johnwinans/2067-Z8S180/fpga/nouveau-vdp99/top.v

//**************************************************************************
//
//    Copyright (C) 2024,2025  John Winans
//
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
//**************************************************************************

`default_nettype none

module top (
    input wire          hwclk,      // 25MHZ oscillator
    input wire          s1_n,
    output wire [7:0]   led,

    input wire [19:0]   a,
    inout wire [7:0]    d,          // bidirectional

    input wire          busack_n,
    output wire         busreq_n,

    output wire         ce_n,
    output wire         oe_n,
    output wire         we_n,

    output wire         dreq1_n,

    input wire          e,
    output wire         extal,
    input wire          phi,

    input wire          halt_n,

    output wire [2:0]   int_n,
    output wire         nmi_n,

    input wire          rd_n,
    input wire          wr_n,
    input wire          iorq_n,
    input wire          mreq_n,
    input wire          m1_n,

    output wire         reset_n,
    input wire          rfsh_n,
    input wire          st,
    input wire          tend1_n,
    output wire         wait_n,

    output wire         sd_mosi,
    output wire         sd_clk,
    output wire         sd_ssel_n,

    input wire          sd_miso,
    input wire          sd_det,

    input wire          joy1_up,
    input wire          joy1_dn,
    input wire          joy1_lt,
    input wire          joy1_rt,
    input wire          joy1_fire,
    input wire          joy1_btn2,

    output  wire [1:0]  vga_red,
    output  wire [1:0]  vga_grn,
    output  wire [1:0]  vga_blu,
    output  wire        vga_hsync,
    output  wire        vga_vsync,

    output  wire [2:0]  aout,       // hack for testing the AY-3-891x

    output wire [15:0]  tp          // handy-dandy test-point outputs
    );

    wire [7:0] vdp_dout;
    wire vdp_irq;

    localparam RAM_START = 20'h1000;

    assign tp = { iorq_wr_tick, iorq_rd_tick, phi, e, iorq_n, we_n, oe_n, ce_n, wr_n, rd_n, mreq_n, m1_n };
    //            93            90            87   84 82      80    78    75    73    63    61      56


    localparam HWCLK_FREQ       = 25000000;

    localparam NUM_BOOT_BRAMS   = 6;                  // Even number due to bug in yosys newer versions!
    localparam NUM_VRAM_BRAMS   = 32-NUM_BOOT_BRAMS;  // 32 total in ICE40HX4/8K, residual = VRAM

    // a boot ROM
    wire [7:0]  rom_data;           // ROM output data bus
    memory #( .RAM_SIZE(NUM_BOOT_BRAMS*512) ) rom ( .rd_clk(phi), .addr(a), .data(rom_data) );

    // consider debouncing s1_n using hwclk (no other clock possible)
    wire reset = ~s1_n || ~pll_locked;      // assert reset when PLL is starting up & unstable
    assign reset_n = ~reset;                // CPU reset

    // When the CPU is reading from the FPGA drive the bus, else tri-state it.
    reg [7:0] dout;                 // what to write to data bus when requested
    reg dbus_out;                   // 1 if the FPGA shoudl drive the data bus
    assign d = dbus_out ? dout : 8'bz;  // a tri-state driver

    reg rom_sel;                    // true when the boot ROM is enabled
    always @(posedge phi)
        if ( reset )
            rom_sel <= 1;               // after a hard reset, the boot ROM is enabled...
        else if ( ioreq_rd_fe_tick )    // until there is a read from IO port 0xfe
            rom_sel <= 0;

    // Determine if the FPGA will drive the data bus and with what
    // the CPU is reading from its data bus.
    always @(*) begin
        dbus_out = 1;
        dout = 8'bx;

        (* parallel_case *)     // no more than one case can match (one-hot)
        case (1)
        mreq_rom:       dout = rom_data;            // boot ROM memory
        ioreq_rd_f0:    dout = ioreq_rd_data;       // gpio input
        ioreq_rd_j3:    dout = ioreq_rd_data;       // J3 input
        ioreq_rd_j4:    dout = ioreq_rd_data;       // J4 input
        ioreq_rd_ay:    dout = ay_dout;       		// ay-3-8910
        ioreq_rd_vdp:   dout = vdp_dout;            // data from the VDP
        default:        dbus_out = 0;
        endcase
    end

    // 18.432MHZ = 57600 (when running at X/2)
    // 18.432MHZ = 115200 (when running at X/1)
    wire        pll_locked;             // true when the PLL has locked to target freq
    pll_25_18432 pll ( .clock_in(hwclk), .clock_out(extal), .locked(pll_locked) );


    // for read cycle: latch value on first phi falling edge after iorq becomes true:
    // fsm counting falling phi when rd is true & enable when count = 0 && iorq is true
    wire    iorq_rd_tick;
    iorq_rd_fsm rd_fsm (.reset(reset), .phi(phi), .iorq(~iorq_n), .rd(~rd_n), .rd_tick(iorq_rd_tick) );

    // for a write cycle: latch value on second phi falling edge after iorq becomes true:
    // fsm counting falling phi when wr is true and enable when count = 1
    wire    iorq_wr_tick;
    iorq_wr_fsm wr_fsm (.reset(reset), .phi(phi), .iorq(~iorq_n), .wr(~wr_n), .wr_tick(iorq_wr_tick) );


    // qualified asynchronous bus enable signals
    wire iorq_rd = ~iorq_n && ~rd_n;
    wire iorq_wr = ~iorq_n && ~wr_n;
    wire mem_rd = ~mreq_n && ~rd_n;
    wire mem_wr = ~mreq_n && ~wr_n;

    // IO address decoders (two variations):
    //  signal       = CPU asynchronous IO cycle
    //  signal_tick  = FPGA ff clock enable synchronized to phi
    //  NOTE: The address bus is stable during the iorq_rd/wr_tick periods.

    // gpio input
    wire ioreq_rd_f0 = iorq_rd && (a[7:0] == 8'hf0);                // gpio input
    wire ioreq_rd_f0_tick = iorq_rd_tick && (a[7:0] == 8'hf0);

//  wire ioreq_wr_f1 = iorq_wr && (a[7:0] == 8'hf1);                // gpio output
    wire ioreq_wr_f1_tick  = iorq_wr_tick && (a[7:0] == 8'hf1);

//  wire ioreq_rd_fe = iorq_rd && (a[7:0] == 8'hfe);                
    wire ioreq_rd_fe_tick = iorq_rd_tick && (a[7:0] == 8'hfe);      // flash select disable access port

    wire ioreq_rd_j3 = iorq_rd && (a[7:0] == 8'ha8);
    wire ioreq_rd_j3_tick = iorq_rd_tick && (a[7:0] == 8'ha8);      // joystick J3

    wire ioreq_rd_j4 = iorq_rd && (a[7:0] == 8'ha9);
    wire ioreq_rd_j4_tick = iorq_rd_tick && (a[7:0] == 8'ha9);      // joystick J4

    // B0 & B1 are the ay registers
    wire ioreq_wr_ay = iorq_wr && (a[7:1] == 8'hb0>>1);
    wire ioreq_rd_ay = iorq_rd && (a[7:1] == 8'hb0>>1);

    // ROM memory address decoder (address bus is 20 bits wide)
    wire mreq_rom = rom_sel && mem_rd && a[19:12] == 0;         // all top MSBs of bottom 4K are zero

    wire [7:0]  ay_dout;
    wire [2:0]  ay3891x_out;

    z80_ay3891x #(
        .CLK_FREQ(HWCLK_FREQ),
        ) ay (
        .reset(reset),
		.phi(phi),
        .clk(hwclk),
        .a0(a[0]),
        .cpu_wr(ioreq_wr_ay),
        .wdata(d),
        .cpu_rd(ioreq_rd_ay),
        .rdata(ay_dout),
        .aout(ay3891x_out)
        );

    assign aout = ay3891x_out;
    //assign aout = {2'b00, |ay3891x_out};    // OR the three channels into only the A channel output bit


    // The GPIO output latch
    reg [7:0] gpio_out;
    always @(negedge phi) begin
        if ( ioreq_wr_f1_tick )
            gpio_out <= d;
    end

    // This should be a 2-always state machine.
    reg [7:0] ioreq_rd_data;            // data value when reading an internal IO port
    always @(negedge phi) begin
        // ioreq_rd_data is an implied latch in here
        // XXX synchronize the joystick inputs at some point
        (* parallel_case *)     // no more than one case can match (one-hot)
        case (1)
        ioreq_rd_f0_tick:   ioreq_rd_data <= {sd_miso,sd_det,6'bx};
        ioreq_rd_j3_tick:   ioreq_rd_data <= { joy1_up, joy1_dn, joy1_rt, joy1_btn2, 1'b1, joy1_lt, ~vdp_irq, joy1_fire };
        ioreq_rd_j4_tick:   ioreq_rd_data <= { joy1_up, joy1_dn, joy1_rt, joy1_btn2, 1'b1, joy1_lt, 1'b1, joy1_fire };  // XXX
        endcase
    end

    assign sd_mosi = gpio_out[0];   // connect the GPIO output bits to the SD card pins
    assign sd_clk  = gpio_out[1];
    assign sd_ssel_n = gpio_out[2];

    assign busreq_n = 1'b1;     // de-assert /BUSREQ
    assign dreq1_n = 1'b1;      // de-assert /DREQ1
    assign int_n = { ~vdp_irq, 2'b11 };
    assign nmi_n = 1'b1;        // de-assert /NMI
    assign wait_n = 1'b1;       // de-assert /WAIT

    // Enable the static RAM on memory cycles when the data bus is driven by the FPGA
    // The address range that is used to enable the SRAM varies depending on if/when
    // the shadow ROM is being enabled.
    assign ce_n = ~(~mreq_n && ~dbus_out );
    assign oe_n = mreq_n | rd_n;
    assign we_n = mreq_n | wr_n;

    wire ioreq_rd_vdp = iorq_rd && (a[7:1] == 7'b1000000);  // true for ports 80 and 81
    wire ioreq_wr_vdp = iorq_wr && (a[7:1] == 7'b1000000);  // true for ports 80 and 81

`ifdef no_sync_vga
    wire [3:0] vdp_color;
    wire vdp_hsync;
    wire vdp_vsync;

    z80_vdp99 #( .VRAM_SIZE(NUM_VRAM_BRAMS*512) ) vdp (
        .reset(reset),
        .phi(phi),
        .pxclk(hwclk),
        .cpu_mode(a[0]),
        .cpu_din(d),
        .cpu_dout(vdp_dout),
        .irq(vdp_irq),
        .cpu_wr(ioreq_wr_vdp),
        .cpu_rd(ioreq_rd_vdp),
        .color(vdp_color),
        .hsync(vdp_hsync),
        .vsync(vdp_vsync)
    );

    // Remap the 4-bit VDP color codes to 6-bit RGB
    color_palette palette (
        .color(vdp_color),
        .red(vga_red),
        .grn(vga_grn),
        .blu(vga_blu)
    );

    assign vga_hsync = ~vdp_hsync;
    assign vga_vsync = ~vdp_vsync;
`else
    z80_vga99 #( .VRAM_SIZE(NUM_VRAM_BRAMS*512) ) vdp (
        .reset(reset),
        .phi(phi),
        .pxclk(hwclk),
        .cpu_mode(a[0]),
        .cpu_din(d),
        .cpu_dout(vdp_dout),
        .irq(vdp_irq),
        .cpu_wr(ioreq_wr_vdp),
        .cpu_rd(ioreq_rd_vdp),
        .red(vga_red),
        .grn(vga_grn),
        .blu(vga_blu),
        .hsync(vga_hsync),
        .vsync(vga_vsync)
    );
`endif

    // show some signals from the GPIO ports on the LEDs for reference
    assign led = {~sd_miso,sd_det,3'b111,~gpio_out[2:0]};

endmodule
