johnwinans/2067-Z8S180/fpga/nouveau-vdp99/z80_vdp99_tb.v

//**************************************************************************
//
//    Copyright (C) 2025  John Winans
//
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
//**************************************************************************

`timescale 1ns/1ns
`default_nettype none

module tb ();

    reg reset       = 1;
    reg phi         = 0;
    reg pxclk       = 0;

    reg iorq        = 0;
    reg rd          = 0;
    reg wr          = 0;
    reg [15:0] a    = 'hz;
    reg [7:0] d     = 'hz;

    reg t1_marker   = 0;    // used to make obvious which are T1 phi clocks


    wire [7:0]   cpu_dout;
    wire [3:0]   color;
    wire hsync;
    wire vsync;
    wire irq;

    z80_vdp99 uut (
        .reset(reset),
        .phi(phi),
        .pxclk(pxclk),
        .cpu_mode(a[0]),
        .cpu_din(d),
        .cpu_dout(cpu_dout),
        .cpu_wr(iorq && wr && (a[7:1] == 7'b1000000)),
        .cpu_rd(iorq && rd && (a[7:1] == 7'b1000000)),
        .color(color),
        .hsync(hsync),
        .vsync(vsync),
        .irq(irq)
    );

    localparam phi_period = (1.0/18432000)*1000000000; // clk1 is running at about 18.432MHZ
    localparam pxclk_period = (1.0/25000000)*1000000000; // clk2 is running at 25MHZ

    always #(phi_period/2) phi = ~phi;
    always #(pxclk_period/2) pxclk = ~pxclk;

    integer i;      // for loop iterator


    // A way to easily write to a VDP register in the test bench
    // to use this, set vdp_reg, and vdp_reg_value and then set do_reg_write true for one phi period
    //      vdp_reg <= 3;
    //      vdp_reg_value <= 12;
    //      do_reg_write <= 1;
    //      @(negedge do_reg_write);        // wait for this to set it back to 0

    reg [2:0]   vdp_reg         = 0;
    reg [7:0]   vdp_reg_value   = 0;
    reg         do_reg_write    = 0;

    always begin
        // wait for a tick on do_reg_write
        while (do_reg_write != 1'b1)
            @(posedge phi);

        @(posedge phi);         // wait for T1 rising of next bus cycle (opcode fetch)
        t1_marker <= 1;
        t1_marker <= #(phi_period) 0;
        @(posedge phi);         // T2 opcode fetch
        @(posedge phi);         // T3 opcode fetch

        // skip the operand fetch as if this were an OUT (nn),A instruction
        @(posedge phi);         // wait for T1 rising of next bus cycle (operand fetch)
        t1_marker <= 1;
        t1_marker <= #(phi_period) 0;
        @(posedge phi);         // T2 operand fetch
        @(posedge phi);         // T3 operand fetch

        // IO write cycle
        @(posedge phi);         // T1 rising
        t1_marker <= 1;
        t1_marker <= #(phi_period) 0;

        @(negedge phi);         // T1 falling
        a <= #20 8'h81;         // address valid after T1 rising and >5ns before IORQ
        d <= #25 vdp_reg_value; // data <25ns after T1 falling and >10ns before WR active
        iorq <= #25 1;          // iorq = <25ns after T1 falling
                                // rd = <25ns after T1 falling
        @(posedge phi);         // T2 rising
        wr <= #25 1;            // <25ns after T2 rising

        @(posedge phi);         // Tw rising
        @(posedge phi);         // T3 rising
        @(negedge phi);         // T3 falling

        iorq <= #1 0;           // iorq <25ns after T3 falling
        wr <= #1 0;             // wr <25ns after T3 falling
                                // rd <25ns after T3 falling

        @(negedge wr)           // be careful that wr does not happen after posedge phi here!!!
        a <= #5 'hz;            // >5ns after iorq & wr trailing
        d <= #10 'hz;           // >10ns after wr trailing



        @(posedge phi);         // wait for T1 rising of next bus cycle (opcode fetch)
        t1_marker <= 1;
        t1_marker <= #(phi_period) 0;
        @(posedge phi);         // T2 opcode fetch
        @(posedge phi);         // T3 opcode fetch

        // skip the operand fetch as if this were an OUT (nn),A instruction
        @(posedge phi);         // wait for T1 rising of next bus cycle (operand fetch)
        t1_marker <= 1;
        t1_marker <= #(phi_period) 0;
        @(posedge phi);         // T2 operand fetch
        @(posedge phi);         // T3 operand fetch

        // IO write cycle
        @(posedge phi);         // T1 rising
        t1_marker <= 1;
        t1_marker <= #(phi_period) 0;


        @(negedge phi);         // T1 falling
        // write to VDP register i
        a <= #20 8'h81;         // address valid after T1 rising and >5ns before IORQ
        d <= #25 8'h80+vdp_reg; // data <25ns after T1 falling and >10ns before WR active
        iorq <= #25 1;          // iorq = <25ns after T1 falling
                                // rd = <25ns after T1 falling
        @(posedge phi);         // T2 rising
        wr <= #25 1;            // <25ns after T2 rising

        @(posedge phi);         // Tw rising
        @(posedge phi);         // T3 rising

        do_reg_write <= 0;      // we will be done on the next rising phi

        @(negedge phi);         // T3 falling

        iorq <= #1 0;           // iorq <25ns after T3 falling
        wr <= #1 0;             // wr <25ns after T3 falling
                                // rd <25ns after T3 falling

        @(negedge wr)           // be careful that wr does not happen after posedge phi here!!!
        a <= #5 'hz;            // >5ns after iorq & wr trailing
        d <= #10 'hz;           // >10ns after wr trailing

    end




    initial begin
        $dumpfile( { `__FILE__, "cd" } );
        $dumpvars;

        // put some useful test data into the VRAM
        $readmemh( "z80_vdp99_tb.ram", uut.vdp.mem.vram );


        reset <= 1;
        #(phi_period*4);
        reset <= 0;
        #(phi_period*4);


        vdp_reg <= 0;
        vdp_reg_value <= 'h00;      // graphics mode 1
        //vdp_reg_value <= 'h02;      // graphics mode 2
        //vdp_reg_value <= 'h00;      // graphics mode 4
        do_reg_write <= 1;
        @(negedge do_reg_write);

        vdp_reg <= 1;
        vdp_reg_value <= 'h60;      // graphics mode 1, enable screen, IE
        //vdp_reg_value <= 'h68;      // graphics mode 4, enable screen, IE
        //vdp_reg_value <= 'h70;      // text mode, enable screen, IE
        //vdp_reg_value <= 'h50;      // text mode, enable screen, IE=0
        //vdp_reg_value <= 'h60;      // graphics mode 2, enable screen, IE
        do_reg_write <= 1;
        @(negedge do_reg_write);

        vdp_reg <= 2;
        vdp_reg_value <= 'h02;      // name table 0x0800 - 0x0bff
        do_reg_write <= 1;
        @(negedge do_reg_write);

        vdp_reg <= 3;
        vdp_reg_value <= 'h30;      // color table 0x0c00 - 0x0c20
        //vdp_reg_value <= 'h80;      // color table 0x2000 - 0x3800 (for mode 2 gfx)
        do_reg_write <= 1;
        @(negedge do_reg_write);

        vdp_reg <= 4;
        vdp_reg_value <= 'h00;      // pattern table 0x0000 - 0x07ff
        do_reg_write <= 1;
        @(negedge do_reg_write);


        vdp_reg <= 5;
        vdp_reg_value <= 'h1a;      // sprite attribute table 0x0d00 - 0x0d7f
        do_reg_write <= 1;
        @(negedge do_reg_write);

        vdp_reg <= 6;
        vdp_reg_value <= 'h02;      // sprite pattern table 0x1000 - 0x17ff
        do_reg_write <= 1;
        @(negedge do_reg_write);


        vdp_reg <= 7;
        vdp_reg_value <= 'h34;      // fg/bg colors
        do_reg_write <= 1;
        @(negedge do_reg_write);



//#(phi_period*100000);
//$finish;

        // wait until an entire frame has completed
        @(negedge vsync);

        // IRQ should have been asserted
        // Read from the VDP status register to see the IRQ status flag on data bus & then be reset

        @(posedge phi);

        @(negedge phi);         // T1 falling
        a <= #20 8'h81;         // address valid after T1 rising and >5ns before IORQ
        iorq <= #25 1;          // iorq = <25ns after T1 falling
        rd <= #25 1;            // rd = <25ns after T1 falling

        @(posedge phi);         // T2 rising
        @(posedge phi);         // Tw rising
        @(posedge phi);         // T3 rising
        @(negedge phi);         // T3 falling
        iorq <= #1 0;           // iorq <25ns after T3 falling
        rd <= #1 0;             // rd <25ns after T3 falling

        @(negedge iorq);
        a <= #5 'hz;            //  >5ns after iorq & rd trailing

        // wait until we can see the second frame begin
        //@(posedge uut.vdp.fsm.row_last);
        @(posedge uut.vdp.vid_active);
        @(posedge uut.vdp.vid_active);
        @(posedge uut.vdp.vid_active);
        @(posedge uut.vdp.vid_active);

        $finish;
    end

endmodule
