johnwinans/2067-Z8S180/fpga/vdp99/vram_tb.v

//**************************************************************************
//
//    Copyright (C) 2025  John Winans
//
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
//**************************************************************************

`timescale 1ns/1ns
`default_nettype none

module tb();

    localparam  VRAM_SIZE = 8192;
    localparam  VRAM_ADDR_WIDTH = $clog2(VRAM_SIZE);

    reg clk             = 0;        // pixel clock
    reg reset           = 0;
    reg wr_tick         = 0;
    reg rd_tick         = 0;
    reg mode            = 0;
    reg [7:0] din       = 'hz;
    reg [VRAM_ADDR_WIDTH-1:0] dma_addr = 'hx;
    reg dma_tick        = 0;

    wire [7:0] dout;

    vram #( .VRAM_SIZE(VRAM_SIZE) ) uut (
        .reset(reset),
        .clk(clk),
        .rd_tick(rd_tick),
        .wr_tick(wr_tick),
        .mode(mode),
        .din(din),
        .dout(dout),
        .dma_addr(dma_addr),
        .dma_rd_tick(dma_tick)
    );

    initial begin
        $dumpfile( { `__FILE__, "cd" } );
        $dumpvars;
    end
    
    localparam clk_period = (1.0/25000000)*1000000000; // clk is running at 25MHZ
    always #(clk_period/2) clk = ~clk;

    integer     i;
    integer     j;
    reg [7:0]   val8;       // a way to truncate the value of i

    initial begin

        #(clk_period*4);
        reset <= 1;
        #(clk_period*4);
        reset <= 0;
        #(clk_period*4);

        @(posedge clk);
        mode <= 1;          // mode 1 = address
        din <= 8'h00;       // address LSB
        wr_tick <= 1;

        @(posedge clk);
        mode <= 0;
        din <= 'hz;
        wr_tick <= 0;

        @(posedge clk);
        mode <= 1;          // mode 1 = address
        din <= 8'h40;       // address MSB (write mode)
        wr_tick <= 1;

        @(posedge clk);
        mode <= 0;
        din <= 'hz;
        wr_tick <= 0;


        // fill the VRAM with some data
        // note that while filling the first time, the read data is 'hx
//       for ( i=0; i<'h2000; i=i+1 ) begin
        for ( i=0; i<'h1fff; i=i+1 ) begin      // leave the last vram byte unset
            @(posedge clk);
            mode <= 0;      // mode 0 = data
            din <= i&'h0ff;
            wr_tick <= 1;

            @(posedge clk);
            mode <= 0;
            din <= 'hz;
            wr_tick <= 0;

            @(posedge clk);
        end

        // Wait to see the read-ahead getting data from the next address.
        // NOTE: This data may be X if the counter is not allowed to wrap around above.
        @(posedge clk);
        @(posedge clk);
        @(posedge clk);     // extra long time here to find easy in the waveform output
        @(posedge clk);
        @(posedge clk);
        @(posedge clk);

        // read it back
        mode <= 1;          // mode 1 = address
        din <= 8'h00;       // address LSB
        wr_tick <= 1;

        @(posedge clk);
        mode <= 1;          // mode 1 = address
        din <= 8'h00;       // address MSB (read mode)
        wr_tick <= 1;

        @(posedge clk);
        mode <= 0;          // mode 0 = data
        din <= 'hz;         // address MSB (read mode)
        wr_tick <= 0;

        // exagerated delay here to illustrate when dout is valid when idle
        @(posedge clk);
        @(posedge clk);

        for ( i=0; i<'h2000; i=i+1 ) begin
            val8 <= i;

//$display( "%8t vram[%4x]:%x", $time, i+'h20f, uut.vram[i+'h20f] );
            @(posedge clk);
            mode <= 0;      // mode 0 = data
            rd_tick <= 1;

            @(posedge clk);
            mode <= 0;
            rd_tick <= 0;

//$display( "%8t vram[%4x]:%x dout=%x i=%x", $time, i, uut.vram[i], dout, val8 );
            if ( dout !== val8 )
                $display( "memory readback failed: %8t vram[%4x]:%x dout:%x !== i:%x", $time, i, uut.vram[i], dout, val8 );

            @(posedge clk);
        end

        @(posedge clk);
        mode <= 0;
        din <= 'hz;
        wr_tick <= 0;
        rd_tick <= 0;
        @(posedge clk);
        @(posedge clk);
        @(posedge clk);




        // make sure that reading the status register will reset the register fsm
        
        // start setting up a new VRAM address
        mode <= 1;          // mode 1 = address
        din <= 8'h99;       // address LSB 
        wr_tick <= 1;
        rd_tick <= 0;

        @(posedge clk);
        // now abort the vram address setup by reading the status register
        mode <= 1;
        wr_tick <= 0;
        rd_tick <= 1;

        @(posedge clk);
        rd_tick <= 0;
        wr_tick <= 0;

        @(posedge clk);
        // now restart the vram address setting
        mode <= 1;          // mode 1 = address
        din <= 8'h11;       // address LSB 
        wr_tick <= 1;

        @(posedge clk);
        mode <= 1;          // mode 1 = address
        din <= 8'h33;       // address MSB (read mode)
        wr_tick <= 1;

        @(posedge clk);
        rd_tick <= 0;
        wr_tick <= 0;
        mode <= 0;
        din <= 'hz;
        
        @(posedge clk);
        @(posedge clk);
        @(posedge clk);
        mode <= 0;
        rd_tick <= 1;       // read 1 vram byte

        @(posedge clk);
        mode <= 0;
        rd_tick <= 0;

        @(posedge clk);
        mode <= 0;
        rd_tick <= 1;       // read a second vram byte

        @(posedge clk);
        mode <= 0;
        rd_tick <= 0;




        // DMA access tests
        @(posedge clk);
        mode <= 0;
        rd_tick <= 0;
        wr_tick <= 0;


        @(posedge clk);
        @(posedge clk);
        @(posedge clk);
        dma_addr <= 'h1100;
        dma_tick <= 1;

        @(posedge clk);
        dma_addr <= 'h1101;
        dma_tick <= 1;
        @(posedge clk);
        dma_addr <= 'h1102;
        dma_tick <= 1;

//        @(posedge clk);
//        dma_addr <= 0;
//        dma_tick <= 0;


        @(posedge clk);
        dma_addr <= 'hx;
        dma_tick <= 0;
        mode <= 0;
        rd_tick <= 1;       // read vram using the CPU interface
        @(posedge clk);
        mode <= 0;
        rd_tick <= 1;       // and another...  (this is illegally fast)
        @(posedge clk);
        mode <= 0;
        rd_tick <= 0;
        dma_addr <= 'h1103;
        dma_tick <= 1;

        // idle for a moment
        @(posedge clk);
        mode <= 0;
        rd_tick <= 0;
        wr_tick <= 0;
        dma_tick <= 0;
        dma_addr <= 'hx;
        din <= 'hz;
        @(posedge clk);
        @(posedge clk);

        @(posedge clk);     // another DMA read to show the address counter NOT advancing
        mode <= 0;
        rd_tick <= 0;
        wr_tick <= 0;
        dma_tick <= 1;
        dma_addr <= 'h1107;
        din <= 'hz;

        @(posedge clk);


        // what happens when BOTH dma_tick and rd_tick are true at the same time?
        mode <= 0;
        rd_tick <= 0;
        wr_tick <= 0;
        dma_tick <= 0;
        dma_addr <= 'hx;
        din <= 'hz;
        @(posedge clk);

        @(posedge clk);
        dma_addr <= 'h1108;
        dma_tick <= 1;
        rd_tick <= 1;

        @(posedge clk);
        mode <= 0;
        rd_tick <= 0;
        wr_tick <= 0;
        dma_tick <= 0;
        dma_addr <= 'hx;
        din <= 'hz;

        // waste time to make waveform easier to read
        @(posedge clk);
        @(posedge clk);
        @(posedge clk);


        // What happens If we assert dma_tick multiple periods with a rd_tick before the last dma_tick?
        // Observation: This is understandable but undesirable to do IRL.
        @(posedge clk);
        dma_addr <= 'h1109;
        dma_tick <= 1;
        rd_tick <= 0;

        @(posedge clk);
        dma_addr <= 'h110a;
        dma_tick <= 1;
        rd_tick <= 1;

        @(posedge clk);
        dma_addr <= 'h110b;
        dma_tick <= 1;
        rd_tick <= 0;



        // idle a while so can see the end of the waveform

        @(posedge clk);
        mode <= 0;
        rd_tick <= 0;
        wr_tick <= 0;
        dma_tick <= 0;
        dma_addr <= 'hx;
        din <= 'hz;

        #(clk_period*20);
        $finish;
    end

endmodule
