johnwinans/2067-Z8S180/fpga/vdp99/sprite.v

//**************************************************************************
//
//    Copyright (C) 2025  John Winans
//
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
//**************************************************************************

`timescale 1ns/1ns
`default_nettype none

/**
* Implement one TI99-style sprite.
*
* Pattern will have 16 bits loaded.  When rendering 8 bits, the LSB will be zero.
* (The TI99 size parameter is not handled here.)
* 1 VDP pixel = 2 pxclk periods.
* Note that mag can double the size to 32x32 max.
***************************************************************************/
module sprite 
    (
    input   wire        reset,          // active high
    input   wire        pxclk,          // 25MHZ VGA clock (2X the VDP clock)

    input   wire        vdp_col0_tick,  // when true, the next col will represent hpos_reg zero
    input   wire        mag,            // true when magnified mode (2X size VDP pixels)
    input   wire [8:0]  hpos,           // 0=left edge, 0xff=off right edge (in VDP pixel units)
    input   wire [15:0] pattern,        // pattern of the current row to render
    input   wire [3:0]  fg_color,       // foreground color
    input   wire        load_tick,      // true when time to load the pattern, hpos, fg_color,...

    output  wire [3:0]  color_out       // set to either fg_color or zero
    );

    reg         active_reg, active_next;            // sprite rendering is active
    reg [1:0]   pxvdp_reg, pxvdp_next;              // counts at pxclk rate
    reg         mag_reg, mag_next;                  // false = 1:1, true = 2:1 (magnify VDP pixels)
    reg [8:0]   hpos_reg, hpos_next;                // 0 = 32 VDP px to left of border
    reg         hpos_phase_reg, hpos_phase_next;    // used to remember if the hpos is even or odd
    reg [15:0]  pattern_reg, pattern_next;          // 16-bit row value that will shift out at hpos_reg
    reg [3:0]   fg_color_reg, fg_color_next;        // the sprite foreground color

    always @(posedge pxclk) begin
        if (reset) begin
            active_reg <= 0;
            pxvdp_reg <= 0;
            mag_reg <= 0;
            hpos_reg <= 0;
            hpos_phase_reg <= 0;
            pattern_reg <= 0;
            fg_color_reg <= 0;
        end else begin
            active_reg <= active_next;
            pxvdp_reg <= pxvdp_next;
            mag_reg <= mag_next;
            hpos_reg <= hpos_next;
            hpos_phase_reg <= hpos_phase_next;
            pattern_reg <= pattern_next;
            fg_color_reg <= fg_color_next;
        end
    end

    always @(*) begin
        active_next = active_reg;
        mag_next = mag_reg;
        hpos_next = hpos_reg;
        hpos_phase_next = hpos_phase_reg;
        pattern_next = pattern_reg;
        fg_color_next = fg_color_reg;

        pxvdp_next = pxvdp_reg+1;           // counts VGA pixels (in spite of the name)

        if (load_tick) begin
            active_next = 0;
            mag_next = mag;
            hpos_next = hpos;
            hpos_phase_next = hpos[0];      // used when smag=1 to shift on even/odd columns
            pattern_next = pattern;
            fg_color_next = fg_color;
        end

        if (vdp_col0_tick) begin
            active_next = 1;                // start counting/rendering the sprite
            pxvdp_next = 0;                 // jam sync the phase so start at zero
        end 
        if (active_reg && pxvdp_reg[0]) begin
            // skip hpos_reg pixels and then start showing the pattern bits
            if (hpos_reg != 0) begin
                hpos_next = hpos_reg-1;
            end else begin
                // mag_reg doubles the size of the pixels, shift 1/2 as often
                if ( ~mag_reg )
                    pattern_next = { pattern_reg[14:0], 1'b0 };
                else if ( pxvdp_reg[1] == ~hpos_phase_reg )         // shifting from an even or odd hpos?
                    pattern_next = { pattern_reg[14:0], 1'b0 };
            end
        end
    end

    // Sprite is showing when active_reg & the pattern_reg MSb is 1.
    // Note: After the sprite is done, pattern_reg will be 0. So no need to 'stop' this.
    assign color_out = (active_reg && hpos_reg==0 && pattern_reg[15]) ? fg_color_reg : 0;

endmodule
