johnwinans/2067-Z8S180/fpga/nouveau-vdp99/color_palette.v

//**************************************************************************
//
//    Copyright (C) 2025  John Winans
//
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
//**************************************************************************

`timescale 1ns/1ns
`default_nettype none

// a color palette for mapping the TI99 colors to a 6-bit RGB dac

module color_palette (
    input wire [3:0]    color,
    output reg [1:0]   red,         // these are reg because I am lazy
    output reg [1:0]   grn,
    output reg [1:0]   blu
    );

    always @(*) begin
        case(color)
        4'h0: begin     // black
            red = 0;
            grn = 0;
            blu = 0;
        end
        4'h1: begin     // black
            red = 0;
            grn = 0;
            blu = 0;
        end
        4'h2: begin     // mid grn
            red = 0;
            grn = 2;
            blu = 0;
        end
        4'h3: begin     // lt grn
            red = 0;
            grn = 3;
            blu = 0;
        end
        4'h4: begin     // drk blu
            red = 0;
            grn = 0;
            blu = 1;
        end
        4'h5: begin     // lt blu
            red = 0;
            grn = 0;
            blu = 3;
        end
        4'h6: begin     // drk red
            red = 1;
            grn = 0;
            blu = 0;
        end
        4'h7: begin     // cyan
            red = 0;
            grn = 3;
            blu = 3;
        end
        4'h8: begin     // med red
            red = 2;
            grn = 0;
            blu = 0;
        end
        4'h9: begin     // lt red
            red = 3;
            grn = 0;
            blu = 0;
        end
        4'ha: begin     // drk yel
            red = 1;
            grn = 1;
            blu = 0;
        end
        4'hb: begin     // lt yel
            red = 3;
            grn = 3;
            blu = 0;
        end
        4'hc: begin     // drk grn
            red = 0;
            grn = 1;
            blu = 0;
        end
        4'hd: begin     // magenta
            red = 3;
            grn = 0;
            blu = 3;
        end
        4'he: begin     // gry
            red = 1;
            grn = 1;
            blu = 1;
        end
        4'hf: begin     // wht
            red = 3;
            grn = 3;
            blu = 3;
        end
        endcase
    end

endmodule
