johnwinans/2067-Z8S180/fpga/vdp99/reg_ifce_tb.v

//**************************************************************************
//
//    Copyright (C) 2025  John Winans
//
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
//**************************************************************************

`timescale 10ns/1ns

module tb();

    reg clk;        // pixel clock
    reg reset;
    reg wr_tick;
    reg rd_tick;
    reg [7:0] din;

    vdp_reg_ifce uut (
        .clk(clk),
        .reset(reset),
        .wr_tick(wr_tick),
        .rd_tick(rd_tick),
        .din(din)
    );

    initial begin
        $dumpfile("reg_ifce_tb.vcd");
        $dumpvars;
    end
    
    always #1 clk = ~clk;

    initial begin
        clk = 0;
        wr_tick = 0;
        rd_tick = 0;
        din = 'hz;
        reset = 1;
        #5;

        reset <= 0;
        #4;

        //#0.3;           // exaggerate the tick changes after the rising edges

        // reg0 = 0xee
        din <= 'hee;
        wr_tick <= 1;
        #2;
        wr_tick <= 0;
        din <= 'hz;
        #2;
        din <= 'h80;     // write into reg 0
        wr_tick <= 1;
        #2;
        wr_tick <= 0;
        din <= 'hz;
        #2;

        // reg3 = 0x33
        din <= 'h33;
        wr_tick <= 1;
        #2;
        wr_tick <= 0;
        din <= 'hz;
        #2;
        din <= 'h83;     // write into reg 3
        wr_tick <= 1;
        #2;
        wr_tick <= 0;
        din <= 'hz;
        #2;

        // rapid-fire writes
        din <= 'h44;
        wr_tick <= 1;
        #2;
        din <= 'h84;
        #2;
        din <= 'h55;
        #2;
        din <= 'h85;
        #2;
        din <= 'h66;
        #2;
        din <= 'h86;
        #2;
        wr_tick <= 0;
        din <= 'hz;
        #4;

        // test rm0 reset the 2-state write register toggler
        din <= 'h22;
        wr_tick <= 1;
        #2;
        wr_tick <= 0;
        din <= 'hz;
        #2;

        rd_tick <= 1;
        #2;
        rd_tick <= 0;
        din <= 'hz;
        #2;

        // make sure it still works (we didn't get it stuck)
        din <= 'h11;
        wr_tick <= 1;
        #2;
        din <= 'h81;
        #2;
        wr_tick <= 0;
        din <= 'hz;
        #2;

        // make sure we can CHANGE a value that has already been written
        din <= 'hf6;
        wr_tick <= 1;
        #2;
        din <= 'h86;
        #2;
        wr_tick <= 0;
        din <= 'hz;
        #2;

        // make sure that rm0 is OK when not done in state 1
        rd_tick <= 1;
        #2;
        rd_tick <= 0;
        din <= 'hz;
        #2;

        // a long wait between successive wm0 writes
        din <= 'h77;
        wr_tick <= 1;
        #2;
        wr_tick <= 0;
        din <= 'hz;
        #6;
        wr_tick <= 1;
        din <= 'h87;
        #2;
        wr_tick <= 0;
        din <= 'hz;
        #2;


        #20;
        $finish;
    end

endmodule
